SmartblocksAT/SmartblocksKiCad/Schematik/Modul4.pdf

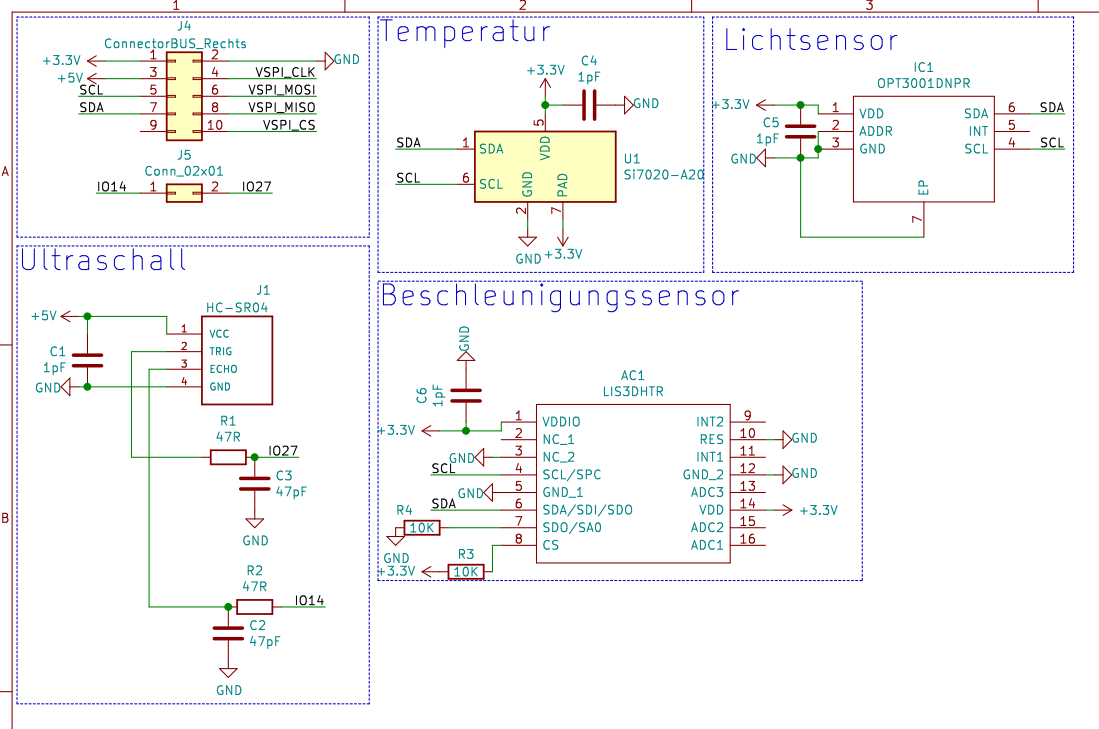
[picture p11: page 1]
